Paulo-Motta-Jr/ESTUDO-DE-CONFORMIDADE-NORMATIVA-E-RETROFIT-DO-SPDA-EM-EDIFICACAO-ACADEMICA/PROJETO AUTOCAD PLANT 3D/Prints/Captura de tela 2025-11-09 194508.png

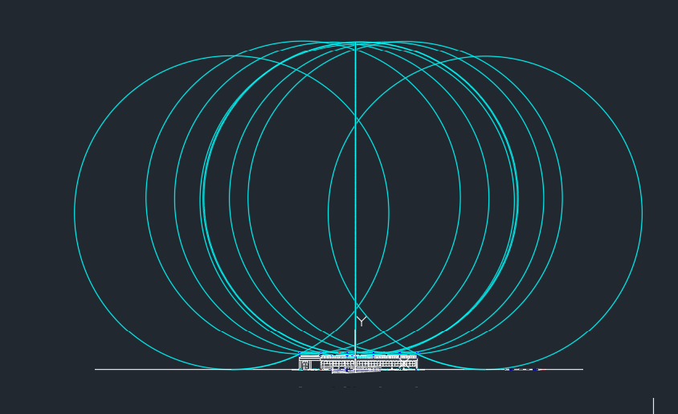
PROJETO AUTOCAD PLANT 3D/Prints/Captura de tela 2025-11-09 194508.png
